mercurieus/esp32s3-rlcd-weather-clock/img/photo1.jpg

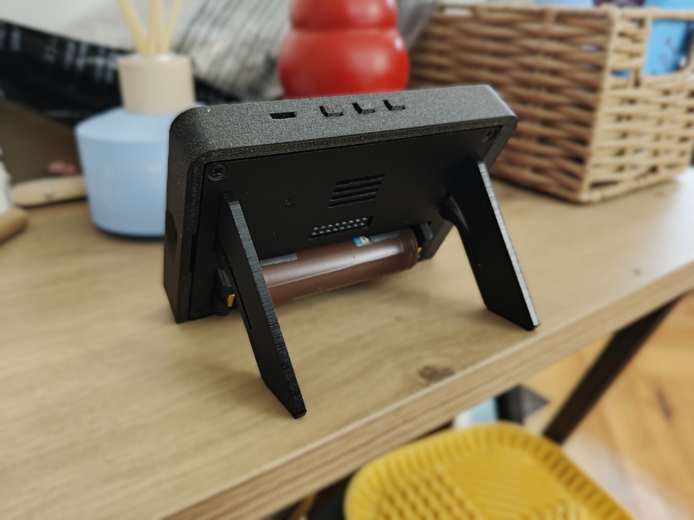
img/photo1.jpg
